usbman01/CH552_usbASP/source/inc/compiler.h

#ifndef COMPILER_H_
/*
   Compiler settings inspired from compiler_defs.h found on the net
   Tasking CC51 is untested. Especially its unclear if it is big endian 
   for each compiler the following macros should be defined
  
   SFR_()    defines a reg in the SFR area 0x80..0xFF
   SBIT_()   defines a single bit within the SFR 
             Note: only valid for SFRs divideable by 8
   SFR16_()  defines a 16 bit sfr in little endian
             Note: the order of access is not guaranted
   NOP()     greates a nop istruction
*/

#ifdef BIG_ENDIAN_
  #undef BIG_ENDIAN_
#endif

#ifdef __RC51__    // Raisonance free now
  #define DATA   data
  #define IDATA  idata
  #define XDATA  xdata
  #define PDATA  pdata
  #define CODE   code
  #define BDATA  bdata
  #define BIT    bit
  #define BIG_ENDIAN_
  
  #define SFR_(name_,adr_)        sfr at adr_ name_
  #define SBIT_(name_,adr_, pos_) sbit  name_ = adr_^pos_
  #define SFR16_(name_,adr_)      sfr16 at adr_ name_
  #define NOP() asm { 0x00 }

#elif __C51__       // keil
  #define DATA   data
  #define IDATA  idata
  #define XDATA  xdata
  #define PDATA  pdata
  #define CODE   code
  #define BDATA  bdata
  #define BIT    bit
  #define BIG_ENDIAN_
  
  #define SFR_(name_,adr_)       sfr   name_ = adr_
  #define SFR16_(name_,adr_)     sfr16 name_ = adr_
  #define SBIT_(name_,adr_,pos_) sbit  name_ = adr_^pos_
  #include <intrins.h>
  #define NOP() _nop_()

#elif __SDCC_mcs51  // SDCC
  #define DATA   __data
  #define IDATA  __idata
  #define XDATA  __xdata
  #define PDATA  __pdata
  #define CODE   __code
  #define BDATA  __bdata
  #define BIT    __bit
//  #define MAKE16(adr_) (((adr_+1) << 8)+adr_) //helper 
  #define SFR_(name_,adr_)       __sfr  __at (adr_) name_
  #define SBIT_(name_,adr_,pos_) __sbit __at (adr_+pos_) name_
  #define SFR16_(name_,addr_)    __sfr16 __at(((addr_+1U)<<8) | addr_) name_
  #define NOP()  __asm__ ("nop")

#elif __IAR_SYSTEMS_ICC__  // iar
  #define DATA   __data
  #define IDATA  __idata
  #define XDATA  __xdata
  #define PDATA  __pdata
  #define CODE   __code
  #define BDATA  __bdata
  #define BIT    __bit
  
  #include <stdbool.h>
  #define SFR_(name_, adr_)        __sfr   __no_init volatile unsigned char name_ @ adr_
  #define SBIT_(name_, adr_, pos_) __bit   __no_init volatile bool name_ @ (adr_+pos_)
  #define SFR16_(name_, adr_)      __sfr   __no_init volatile unsigned int  name_ @ adr_
  #define NOP()  asm ("nop")

#elif _CC51               //tasking not tested at all
  #define DATA   _data
  #define IDATA  _idat
  #define XDATA  _xdat
  #define PDATA  _pdat
  #define CODE   _rom
  #define BDATA  _bdat
  #define BIT    _bit
  #define BIG_ENDIAN_      //not shure but keyword _little inticades it
 
  #define SFR_(name_, adr_)        _sfrbyte name_ _at(adr_)
  #define SBIT_(name_, adr_, pos_) _sfrbit  name_ _at(adr_+pos_)
  #define SFR16_(name_, adr_)      _sfrword _little name_ _at(adr_)
  extern void _nop (void);
  #define NOP() _nop()  
#elif
  #error "Error Compiler unknown"  
#endif

#define COMPILER_H_
#endif
